tudor205/Gas-Leakage-System/Hardware/Arduino 1.kicad_sch

## KiCad design Hardware/Arduino 1.kicad_sch (2026-04-10)

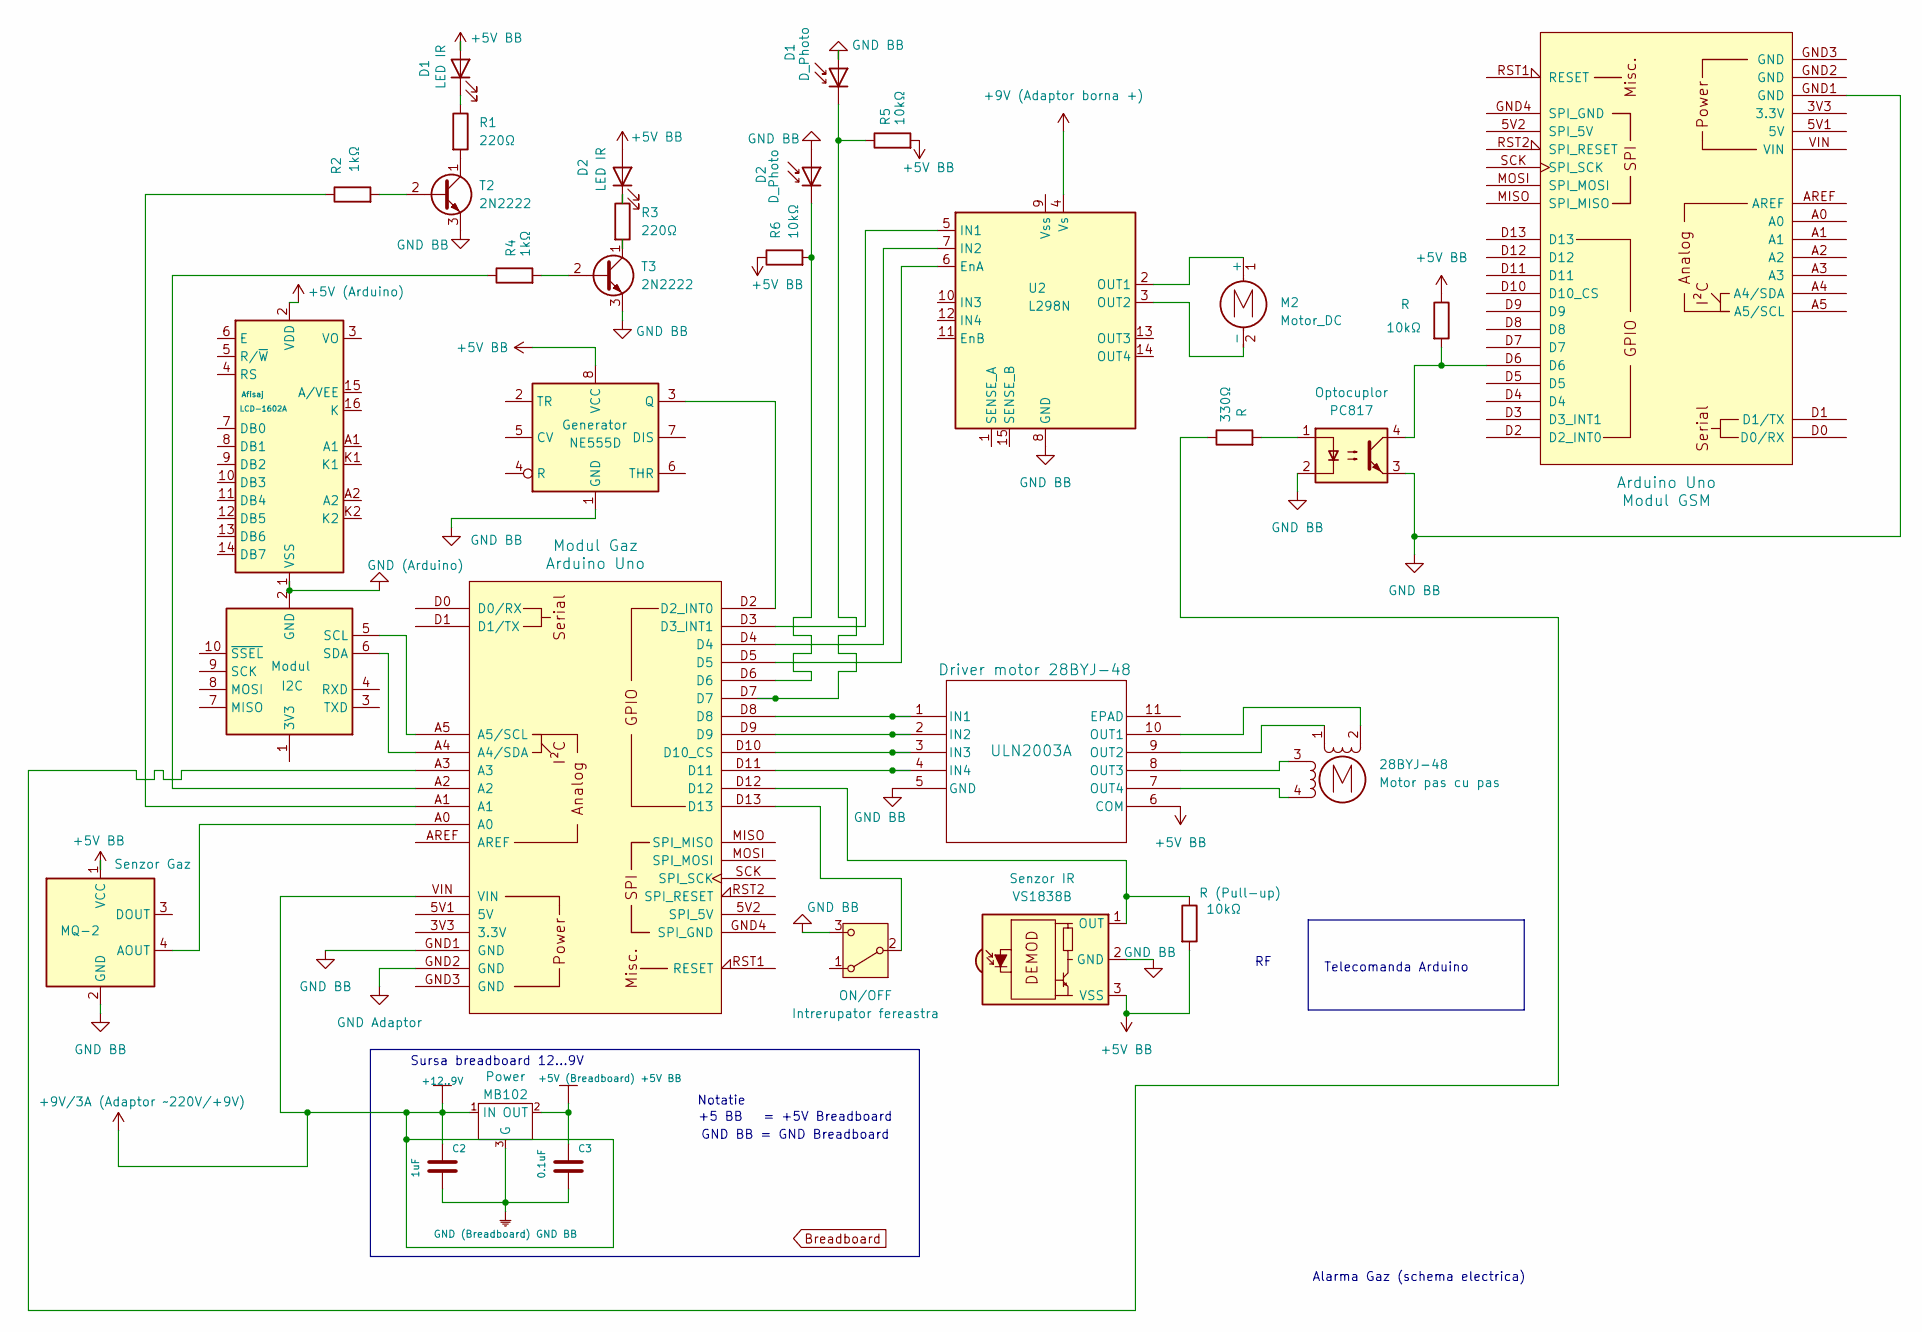
[picture p6: schematic Arduino 1.kicad_sch]

Parts:
1kΩ: R2
28BYJ-48: Motor pas cu pas
330Ω: R
Afisaj: LCD-1602A; LCD-016N002L
C2: 1uF; 0603C
C3: 0.1uF; 0603C
D1: D_Photo
D2: LED IR
Driver motor 28BYJ-48: ULN2003A; U-DFN3030-10_DIO
Generator: NE555D; SOIC-8_3.9x4.9mm_P1.27mm
Intrerupator fereastra: ON/OFF
M2: Motor_DC
Modul: I2C
Modul GSM: Arduino Uno; Arduino_Uno_R2_Shield
Modul Gaz: Arduino Uno; Arduino_Uno_R2_Shield
Optocuplor: PC817; DIP-4_W7.62mm
Power: MB102; AS7805ADTR
R, R5, R6: 10kΩ
R1, R3: 220Ω
R4: 1kΩ
R (Pull-up): 10kΩ
Senzor Gaz: MQ-2; MQ-6
Senzor IR: VS1838B; Vishay_MINICAST-3Pin
T2, T3: 2N2222; TO-92_Inline
U2: L298N; TO-220-15_P2.54x5.08mm_StaggerOdd_Lead4.58mm_Vertical

Connections:
+5V (Arduino): Afisaj.2 (VDD)
+5V (Breadboard) +5V BB: C3.2, Power.2 (OUT)
+5V BB: D1.2 (A), D2.2 (A), Driver motor 28BYJ-48.6 (COM), Generator.8 (VCC), R.1, R5.2, R6.1, R (Pull-up).2, Senzor Gaz.1 (VCC), Senzor IR.3 (VSS)
+9V (Adaptor borna +): U2.4 (Vs)
+12..9V: C2.2, Modul Gaz.VIN, Power.1 (IN)
GND (Arduino): Afisaj.1 (VSS), Modul.2 (GND)
GND (Breadboard) GND BB: C2.1, C3.1, Power.3 (G)
GND Adaptor: Modul Gaz.GND2 (GND)
GND BB: D1.2 (A), D2.2 (A), Driver motor 28BYJ-48.5 (GND), Generator.1 (GND), Intrerupator fereastra.3 (C), Modul GSM.GND1 (GND), Modul Gaz.GND1 (GND), Optocuplor.2, Optocuplor.3, Senzor Gaz.2 (GND), Senzor IR.2 (GND), T2.3 (E), T3.3 (E), U2.8 (GND)
unnamed: 1kΩ.1, Modul Gaz.A1
unnamed: 1kΩ.2, T2.2 (B)
unnamed: 28BYJ-48.1, Driver motor 28BYJ-48.9 (OUT2)
unnamed: 28BYJ-48.2 (-), Driver motor 28BYJ-48.10 (OUT1)
unnamed: 28BYJ-48.3, Driver motor 28BYJ-48.8 (OUT3)
unnamed: 28BYJ-48.4, Driver motor 28BYJ-48.7 (OUT4)
unnamed: 330Ω.1, Modul Gaz.A3
unnamed: 330Ω.2, Optocuplor.1
unnamed: D1.1 (K), Modul Gaz.D7, R1.1, R5.1
unnamed: D2.1 (K), Modul Gaz.D6, R3.1, R6.2
unnamed: Driver motor 28BYJ-48.1 (IN1), Modul Gaz.D8
unnamed: Driver motor 28BYJ-48.2 (IN2), Modul Gaz.D9
unnamed: Driver motor 28BYJ-48.3 (IN3), Modul Gaz.D10 (D10_CS)
unnamed: Driver motor 28BYJ-48.4 (IN4), Modul Gaz.D11
unnamed: Generator.3 (Q), Modul Gaz.D2 (D2_INT0)
unnamed: Intrerupator fereastra.2 (B), Modul Gaz.D13
unnamed: M2.1 (+), U2.2 (OUT1)
unnamed: M2.2 (-), U2.3 (OUT2)
unnamed: Modul GSM.D6, Optocuplor.4, R.2
unnamed: Modul Gaz.A0, Senzor Gaz.4 (AOUT)
unnamed: Modul Gaz.A2, R4.1
unnamed: Modul Gaz.D3 (D3_INT1), U2.5 (IN1)
unnamed: Modul Gaz.D4, U2.7 (IN2)
unnamed: Modul Gaz.D5, U2.6 (EnA)
unnamed: Modul Gaz.D12, R (Pull-up).1, Senzor IR.1 (OUT)
unnamed: Modul.5 (SCL), Modul Gaz.A5 (A5/SCL)
unnamed: Modul.6 (SDA), Modul Gaz.A4 (A4/SDA)
unnamed: R1.2, T2.1 (C)
unnamed: R3.2, T3.1 (C)
unnamed: R4.2, T3.2 (B)

Notes on the sheet:
Sursa breadboard 12...9V
Alarma Gaz (schema electrica)
Notatie
Telecomanda Arduino
+5 BB = +5V Breadboard
GND BB = GND Breadboard
