tudor205/Gas-Leakage-System/Hardware/Arduino 2 (GSM).kicad_sch

## KiCad design Hardware/Arduino 2 (GSM).kicad_sch (2026-04-10)

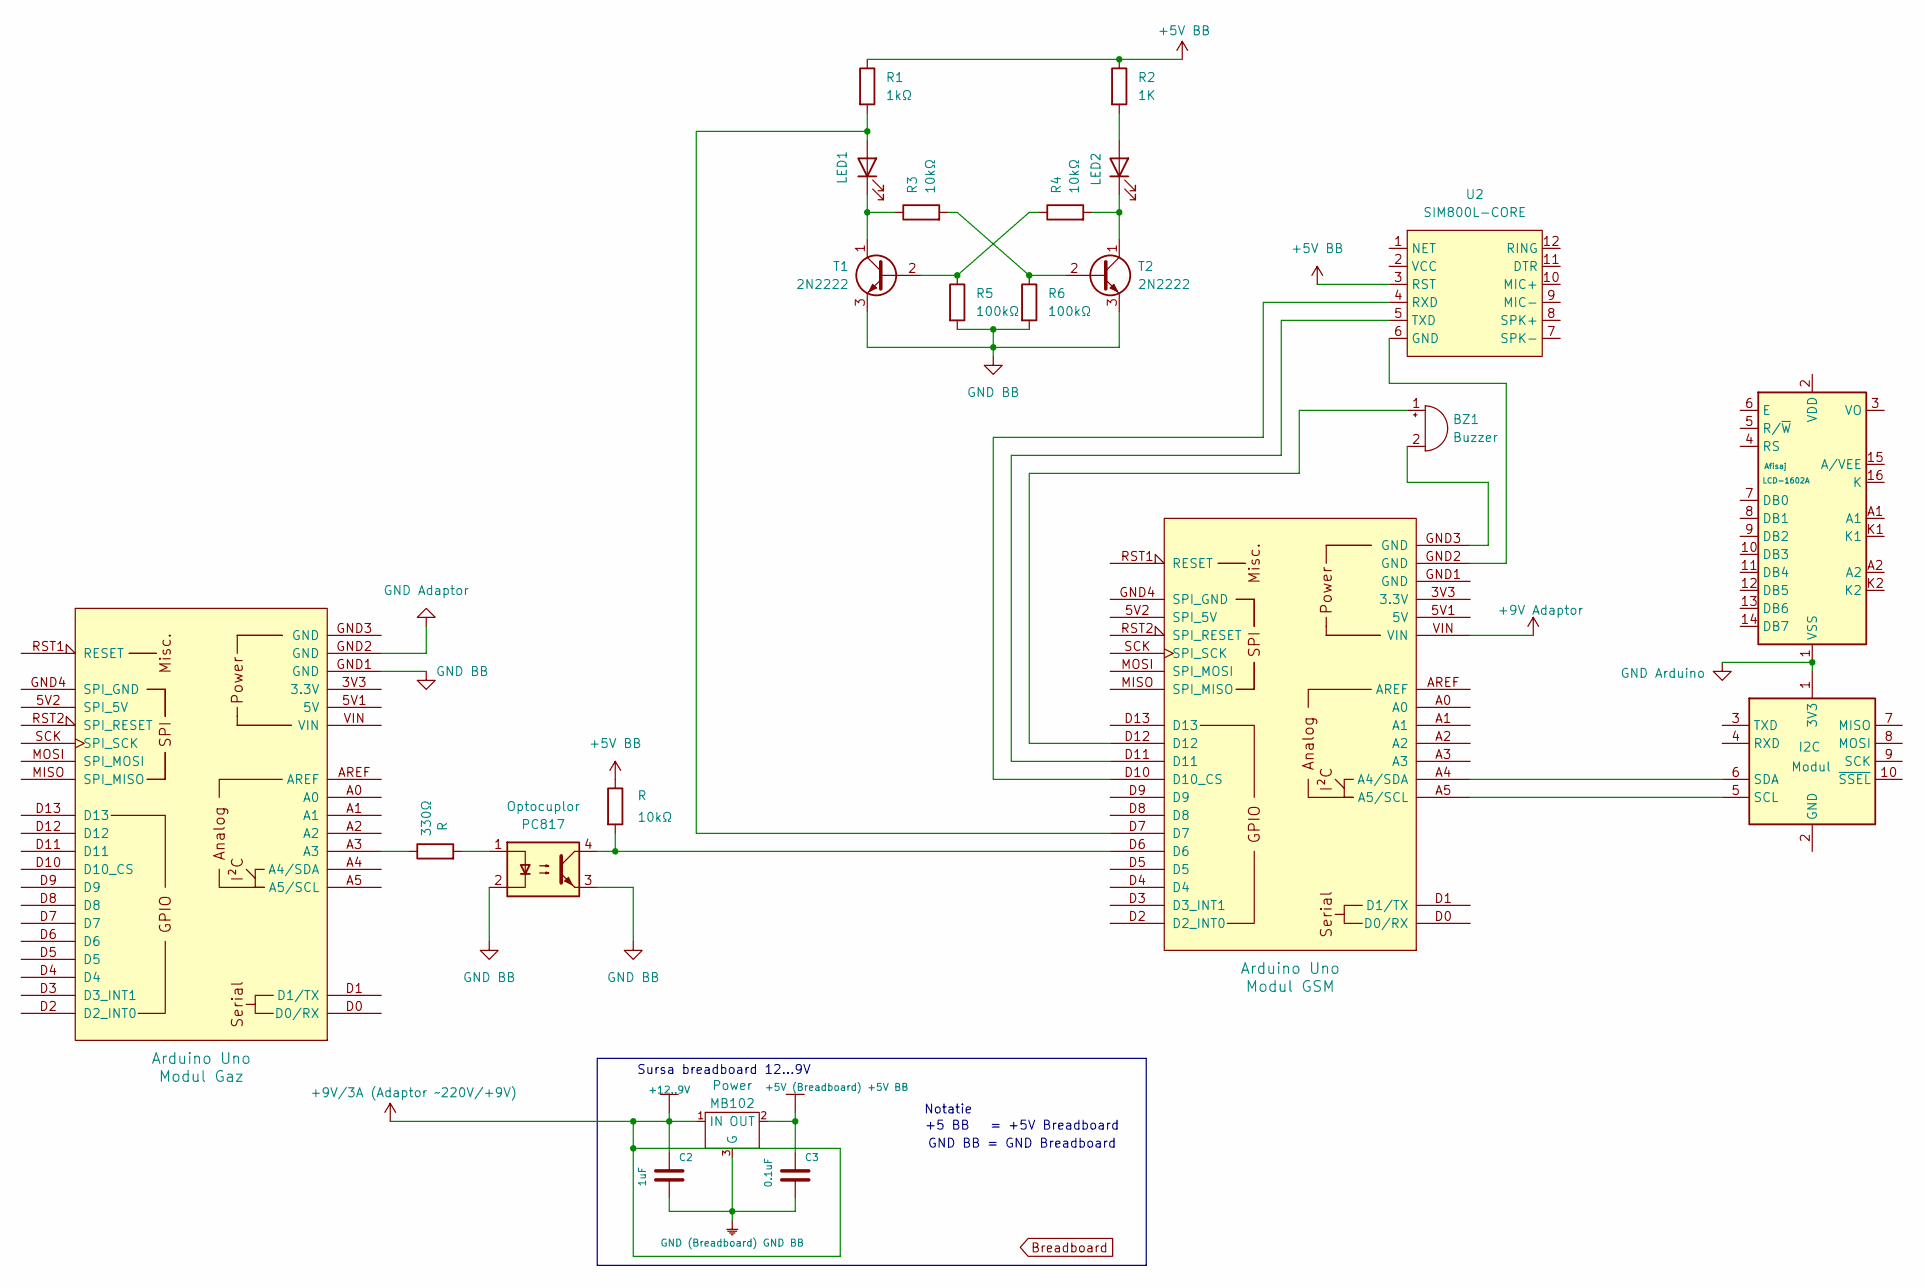
[picture p7: schematic Arduino 2 (GSM).kicad_sch]

Parts:
330Ω: R
Afisaj: LCD-1602A; LCD-016N002L
BZ1: Buzzer
C2: 1uF; 0603C
C3: 0.1uF; 0603C
Modul: I2C
Modul GSM: Arduino Uno; Arduino_Uno_R2_Shield
Modul Gaz: Arduino Uno; Arduino_Uno_R2_Shield
Optocuplor: PC817; DIP-4_W7.62mm
Power: MB102; AS7805ADTR
R, R3, R4: 10kΩ
R1: 1kΩ
R2: 1K
R5, R6: 100kΩ
T1, T2: 2N2222; TO-92_Inline
U2: SIM800L-CORE

Connections:
+5V (Breadboard) +5V BB: C3.2, Power.2 (OUT)
+5V BB: R.1, R1.1, R2.1, U2.3 (RST)
+9V Adaptor: Modul GSM.VIN
+12..9V: C2.2, Power.1 (IN)
GND (Breadboard) GND BB: C2.1, C3.1, Power.3 (G)
GND Adaptor: Modul Gaz.GND2 (GND)
GND Arduino: Afisaj.1 (VSS), Modul.1 (3V3)
GND BB: Modul Gaz.GND1 (GND), Optocuplor.2, Optocuplor.3, R5.2, R6.2, T1.3 (E), T2.3 (E)
unnamed: 330Ω.1, Modul Gaz.A3
unnamed: 330Ω.2, Optocuplor.1
unnamed: BZ1.1 (+), Modul GSM.D12
unnamed: BZ1.2 (-), Modul GSM.GND3 (GND)
unnamed: Modul GSM.D6, Optocuplor.4, R.2
unnamed: Modul GSM.D7, R1.2
unnamed: Modul GSM.D10 (D10_CS), U2.4 (RXD)
unnamed: Modul GSM.D11, U2.5 (TXD)
unnamed: Modul GSM.GND2 (GND), U2.6 (GND)
unnamed: Modul.5 (SCL), Modul GSM.A5 (A5/SCL)
unnamed: Modul.6 (SDA), Modul GSM.A4 (A4/SDA)
unnamed: R3.1, T1.1 (C)
unnamed: R3.2, R6.1, T2.2 (B)
unnamed: R4.1, R5.1, T1.2 (B)
unnamed: R4.2, T2.1 (C)

Notes on the sheet:
Sursa breadboard 12...9V
+5 BB = +5V Breadboard
Notatie
GND BB = GND Breadboard
